cxrphly/line-bot/oled_ui.cpp

#include "OLED_UI.h"
#include "Config.h"
#include "gamepad.h"

const unsigned char epd_bitmap_pixil_frame_0_1_ [] PROGMEM = {
	0x00, 0x00, 0x00, 0x00, 0x00, 0x00, 0x00, 0x00, 0x00, 0x00, 0x00, 0x00, 0x00, 0x00, 0x00, 0x00, 
	0x00, 0x00, 0x00, 0x00, 0x00, 0x00, 0x00, 0x00, 0x00, 0x00, 0x00, 0x00, 0x00, 0x00, 0x00, 0x00, 
	0x00, 0x00, 0x00, 0x00, 0x00, 0x00, 0x00, 0x00, 0x00, 0x00, 0x00, 0x00, 0x00, 0x00, 0x00, 0x00, 
	0x00, 0x00, 0x00, 0x00, 0x00, 0x00, 0x00, 0x00, 0x00, 0x00, 0x00, 0x00, 0x00, 0x00, 0x00, 0x00, 
	0x00, 0x00, 0x00, 0x00, 0x00, 0x00, 0x00, 0x00, 0x00, 0x00, 0x00, 0x00, 0x00, 0x00, 0x00, 0x00, 
	0x00, 0x00, 0x00, 0x00, 0x00, 0x00, 0x00, 0x00, 0x00, 0x00, 0x00, 0x00, 0x00, 0x00, 0x00, 0x00, 
	0x00, 0x00, 0x00, 0x00, 0x00, 0x00, 0x00, 0x00, 0x00, 0x00, 0x00, 0x00, 0x00, 0x00, 0x00, 0x00, 
	0x00, 0x00, 0x00, 0x00, 0x00, 0x00, 0x00, 0x00, 0x00, 0x00, 0x00, 0x00, 0x00, 0x00, 0x00, 0x00, 
	0x00, 0x00, 0x00, 0x00, 0x00, 0x00, 0x00, 0x00, 0x00, 0x00, 0x00, 0x00, 0x00, 0x00, 0x00, 0x00, 
	0x00, 0x00, 0x00, 0x00, 0x00, 0x00, 0x00, 0x00, 0x00, 0x00, 0x00, 0x00, 0x00, 0x00, 0x00, 0x00, 
	0x04, 0x00, 0x00, 0x00, 0x00, 0x00, 0x00, 0x00, 0x00, 0x00, 0x00, 0x06, 0x00, 0x00, 0x00, 0x00, 
	0x07, 0x00, 0x00, 0x00, 0x00, 0x00, 0x00, 0x00, 0x00, 0x00, 0x00, 0x1e, 0x00, 0x00, 0x00, 0x00, 
	0x03, 0xe0, 0x00, 0x1c, 0x00, 0x00, 0x00, 0x00, 0x00, 0x00, 0x00, 0x7c, 0x00, 0x00, 0x00, 0xe0, 
	0x00, 0xfc, 0x00, 0x0f, 0x00, 0x00, 0x00, 0x00, 0x00, 0x00, 0x00, 0xf8, 0x00, 0x00, 0x07, 0xc0, 
	0x00, 0x7f, 0x00, 0x0f, 0xc0, 0x00, 0x00, 0x00, 0x00, 0x00, 0x03, 0xf0, 0x00, 0x00, 0x3f, 0x80, 
	0x00, 0x3f, 0xe0, 0x07, 0xe0, 0x20, 0x00, 0x80, 0x00, 0x00, 0x07, 0xf0, 0x00, 0x00, 0xfe, 0x00, 
	0x00, 0x1f, 0xfc, 0x03, 0xe0, 0x20, 0x01, 0xc0, 0x00, 0x00, 0x07, 0xe0, 0x00, 0x07, 0xfc, 0x00, 
	0x00, 0x0f, 0xff, 0x81, 0xf0, 0x20, 0x01, 0xf0, 0x00, 0x00, 0x0f, 0xc0, 0x0c, 0x1f, 0xf8, 0x00, 
	0x00, 0x03, 0xff, 0xe0, 0xf8, 0x30, 0x00, 0xf0, 0x00, 0x00, 0x0f, 0x80, 0x7c, 0x3f, 0xf0, 0x00, 
	0x00, 0x01, 0xff, 0xfc, 0xf8, 0x30, 0x00, 0xf0, 0x00, 0x04, 0x1f, 0x00, 0xf8, 0x7c, 0xc0, 0x00, 
	0x00, 0x00, 0x1f, 0xff, 0x78, 0x30, 0x00, 0xf1, 0x80, 0x09, 0x9e, 0x43, 0xf8, 0xf0, 0x00, 0x00, 
	0x00, 0x00, 0x07, 0xff, 0xb8, 0x36, 0x38, 0xf3, 0xc0, 0x1b, 0xb9, 0xe3, 0xf1, 0xe0, 0x00, 0x00, 
	0x00, 0x00, 0x01, 0xdf, 0xdc, 0x37, 0x3c, 0xf6, 0xe0, 0x7f, 0xe7, 0xf7, 0xe3, 0xc0, 0x00, 0x00, 
	0x00, 0x00, 0x00, 0x0f, 0x0e, 0x37, 0x1e, 0x6c, 0x71, 0xf7, 0x7c, 0x6f, 0xe7, 0x80, 0x00, 0x00, 
	0x00, 0x00, 0x00, 0x1c, 0x0e, 0x37, 0x9e, 0x68, 0x77, 0xe7, 0xd8, 0xde, 0xcf, 0x00, 0x00, 0x00, 
	0x00, 0x00, 0x00, 0x0c, 0x07, 0x37, 0xff, 0x68, 0x76, 0x0f, 0xb0, 0xfc, 0xde, 0x00, 0x00, 0x00, 
	0x00, 0x00, 0x00, 0x1e, 0x03, 0x37, 0xff, 0x68, 0x32, 0x0f, 0xe1, 0xb9, 0x9c, 0x00, 0x00, 0x00, 
	0x00, 0x00, 0x00, 0x0f, 0xe1, 0xb5, 0xff, 0xe8, 0x02, 0x1f, 0x47, 0x71, 0x30, 0x00, 0x00, 0x00, 
	0x00, 0x00, 0x00, 0x07, 0xf0, 0xf4, 0xfd, 0xed, 0xfb, 0x9f, 0x8f, 0xe3, 0x60, 0x00, 0x00, 0x00, 
	0x00, 0x00, 0x00, 0x01, 0xc0, 0xf4, 0xfc, 0xfc, 0xf6, 0x1f, 0x8f, 0xc3, 0xc0, 0x00, 0x00, 0x00, 
	0x00, 0x00, 0x00, 0x00, 0xc0, 0x74, 0x7c, 0xfc, 0x7e, 0x3d, 0xff, 0x87, 0x80, 0x00, 0x00, 0x00, 
	0x00, 0x00, 0x00, 0x00, 0x61, 0xb7, 0x78, 0x76, 0x67, 0x3d, 0xf3, 0x87, 0x80, 0x00, 0x00, 0x00, 
	0x00, 0x00, 0x00, 0x00, 0x7f, 0x9f, 0x78, 0x73, 0xe3, 0xf0, 0x87, 0x0f, 0x00, 0x00, 0x00, 0x00, 
	0x00, 0x00, 0x00, 0x07, 0xfc, 0x06, 0x30, 0x31, 0xa0, 0x7f, 0x0e, 0x0e, 0x00, 0x00, 0x00, 0x00, 
	0x00, 0x00, 0x00, 0x07, 0xe0, 0x04, 0x30, 0x10, 0x20, 0x3f, 0xc8, 0x0c, 0x00, 0x00, 0x00, 0x00, 
	0x00, 0x00, 0x00, 0x07, 0x80, 0x00, 0x10, 0x00, 0x20, 0x00, 0x10, 0x00, 0x00, 0x00, 0x00, 0x00, 
	0x00, 0x00, 0x00, 0x07, 0x80, 0x00, 0x10, 0x00, 0x00, 0x00, 0x20, 0x00, 0x00, 0x00, 0x00, 0x00, 
	0x00, 0x00, 0x00, 0x06, 0x00, 0x00, 0x00, 0x00, 0x00, 0x00, 0x40, 0x00, 0x00, 0x00, 0x00, 0x00, 
	0x00, 0x00, 0x00, 0x00, 0x00, 0x00, 0x00, 0x00, 0x00, 0x00, 0x00, 0x00, 0x00, 0x00, 0x00, 0x00, 
	0x00, 0x00, 0x00, 0x00, 0x00, 0x00, 0x00, 0x00, 0x00, 0x00, 0x00, 0x00, 0x00, 0x00, 0x00, 0x00, 
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
};
const int epd_bitmap_allArray_LEN = 1;
const unsigned char* epd_bitmap_allArray[1] = {
  epd_bitmap_pixil_frame_0_1_
};


void drawProgressBar(int x, int y, int width, int height, int value, int maxValue) {
    int filled = map(value, 0, maxValue, 0, width);
    display.drawRect(x, y, width, height, SSD1306_WHITE);
    if (filled > 2){
        display.fillRect(x + 1, y + 1, filled - 2, height - 2, SSD1306_WHITE);
    }
}

void showSplashScreen() {
    display.clearDisplay();
    display.setTextSize(1);
    display.setTextColor(SSD1306_WHITE);

    int16_t x, y;
    uint16_t w, h;
    display.getTextBounds("Aguardando controle", 0, 0, &x, &y, &w, &h);
    display.setCursor((SCREEN_WIDTH - w) / 2, 2);
    display.println("Aguardando controle");

    display.drawBitmap(0, 16, epd_bitmap_pixil_frame_0_1_, SCREEN_WIDTH, 48, SSD1306_WHITE);
    display.display();
}

void showMainMenu() {
    display.clearDisplay();
    display.setTextSize(1);
    display.setTextColor(SSD1306_WHITE);

    int16_t x, z;
    uint16_t w, h;
    display.getTextBounds("Menu:", 0, 0, &x, &z, &w, &h);
    display.setCursor((SCREEN_WIDTH - w) / 2, 2);
    display.println("Menu:");

    for (int i = 0; i < menuItemCount; i++) {
        display.setCursor(10, 16 + i * 10);
        display.print(i == menuIndex ? "> " : "  ");
        display.print(menuItems[i]);
        if (i == 1) display.print(controllerModeActive ? " [X]" : " [ ]");
        display.println();
    }
    display.display();
}

void showLineFollowerMenu() {
    display.clearDisplay();
    display.setTextSize(1);
    display.setTextColor(SSD1306_WHITE);

    int16_t x, z;
    uint16_t w, h;
    display.getTextBounds("Seguidor de linha", 0, 0, &x, &z, &w, &h);
    display.setCursor((SCREEN_WIDTH - w) / 2, 2);
    display.println("Seguidor de linha");

    for (int i = 0; i < lfMenuItemCount; i++) {
        display.setCursor(10, 16 + i * 10);
        display.print(i == lfMenuIndex ? "> " : "  ");
        display.print(lfMenuItems[i]);
        if (i == 0) display.print(lineFollowerActive ? " [X]" : " [ ]");
        display.println();
    }
    display.display();
}

void showConfigMenu() {
    display.clearDisplay();
    display.setTextSize(1);
    display.setTextColor(SSD1306_WHITE);

    int16_t x, z;
    uint16_t w, h;
    display.getTextBounds("Config Menu", 0, 0, &x, &z, &w, &h);
    display.setCursor((SCREEN_WIDTH - w) / 2, 2);
    display.println("Config Menu");

    for (int i = 0; i < cfgMenuItemCount; i++) {
        display.setCursor(10, 16 + i * 10);
        display.print(i == cfgMenuIndex ? "> " : "  ");
        display.print(cfgMenuItems[i]);

        char buf[10];

        if (strcmp(cfgMenuItems[i], "Kp") == 0) {
            dtostrf(Kp, 4, 2, buf); display.print(" : "); display.print(buf);
        }
        else if (strcmp(cfgMenuItems[i], "Ki") == 0) {
            dtostrf(Ki, 4, 2, buf); display.print(" : "); display.print(buf);
        }
        else if (strcmp(cfgMenuItems[i], "Kd") == 0) {
            dtostrf(Kd, 4, 2, buf); display.print(" : "); display.print(buf);
        }
        else if (strcmp(cfgMenuItems[i], "Treshold") == 0) {
            itoa(threshold, buf, 10); display.print(" : "); display.print(buf);
        }
        else if (strcmp(cfgMenuItems[i], "MaxSpeed") == 0) {
            itoa(maxSpeed, buf, 10); display.print(" : "); display.print(buf);
        }

        display.println();
    }
    display.display();
}


void showControllerInfo(ControllerPtr ctl) {
    display.clearDisplay();
    display.setTextSize(1);
    display.setTextColor(SSD1306_WHITE);

    int16_t x, z;
    uint16_t w, h;
    display.getTextBounds("Eixos e Gatilhos", 0, 0, &x, &z, &w, &h);
    display.setCursor((SCREEN_WIDTH - w) / 2, 2);
    display.println("Eixos e Gatilhos");

    int y = 14;
    const int lineHeight = 8;

    display.setCursor(0, y);
    display.print("LX:"); 
    drawProgressBar(24, y, 100, 6, ctl->axisX() + 512, 1023);
    y += lineHeight;

    display.setCursor(0, y);
    display.print("LY:");
    drawProgressBar(24, y, 100, 6, ctl->axisY() + 512, 1023);
    y += lineHeight;

    display.setCursor(0, y);
    display.print("RX:");
    drawProgressBar(24, y, 100, 6, ctl->axisRX() + 512, 1023);
    y += lineHeight;

    display.setCursor(0, y);
    display.print("RY:");
    drawProgressBar(24, y, 100, 6, ctl->axisRY() + 512, 1023);
    y += lineHeight;

    display.setCursor(0, y);
    display.print("LT:");
    drawProgressBar(24, y, 100, 6, ctl->brake(), 1023);
    y += lineHeight;

    display.setCursor(0, y);
    display.print("RT:");
    drawProgressBar(24, y, 100, 6, ctl->throttle(), 1023);

    display.display();
}

void showButtonsInfo(ControllerPtr ctl) {
    display.clearDisplay();
    display.setTextSize(1);
    display.setTextColor(SSD1306_WHITE);

    int16_t x, z;
    uint16_t w, h;
    
    display.getTextBounds("Botoes ativos:", 0, 0, &x, &z, &w, &h);
    display.setCursor((SCREEN_WIDTH - w) / 2, 2);
    display.println("Botoes ativos:");
    display.setCursor(0, 30);
    display.println(getPressedButtons(ctl));
    display.display();
}
